Kamaro-Engineering/MiniRobot/doc/DSC_0265.JPG

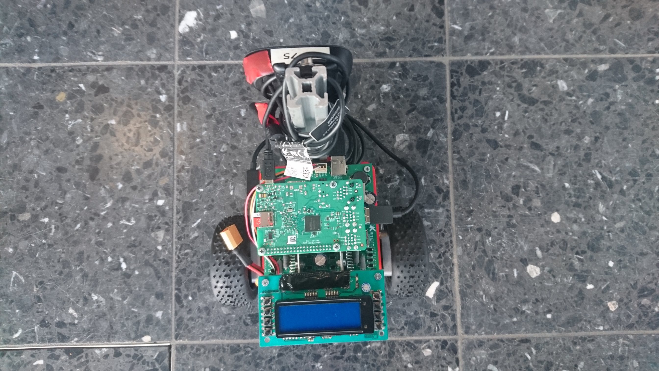
doc/DSC_0265.JPG
