Kamaro-Engineering/MiniRobot/doc/DSC_0266.JPG

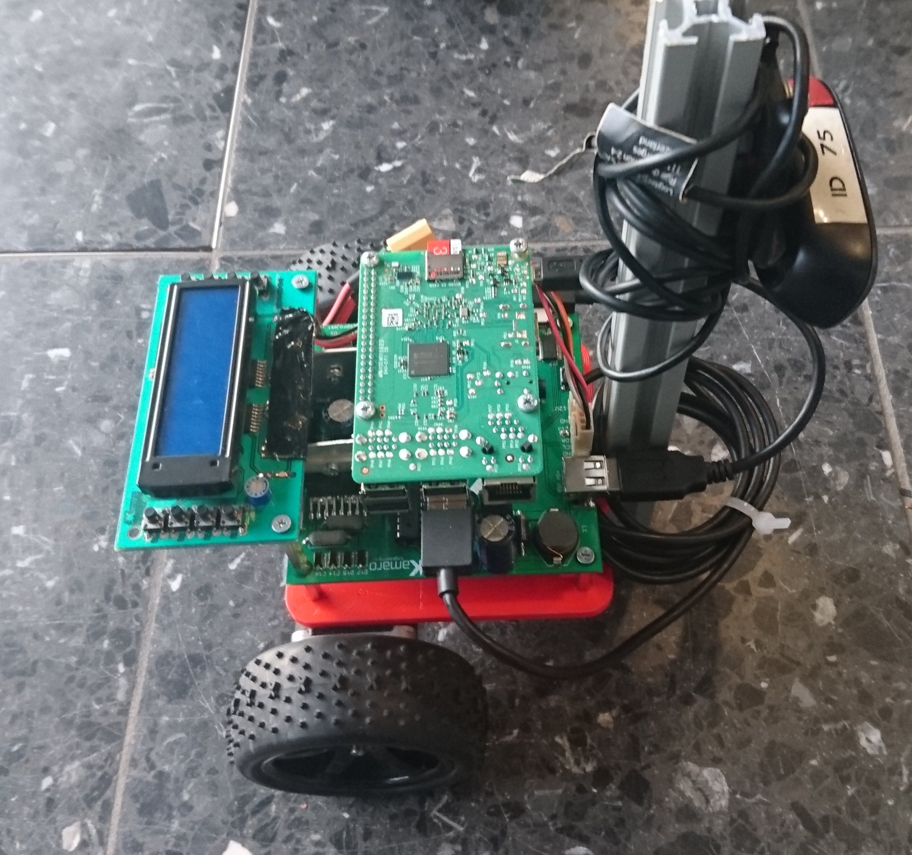
doc/DSC_0266.JPG
